Roman-Ivanitch/Project.9.class/dimensional_drawing/gusset/плохой.jpg

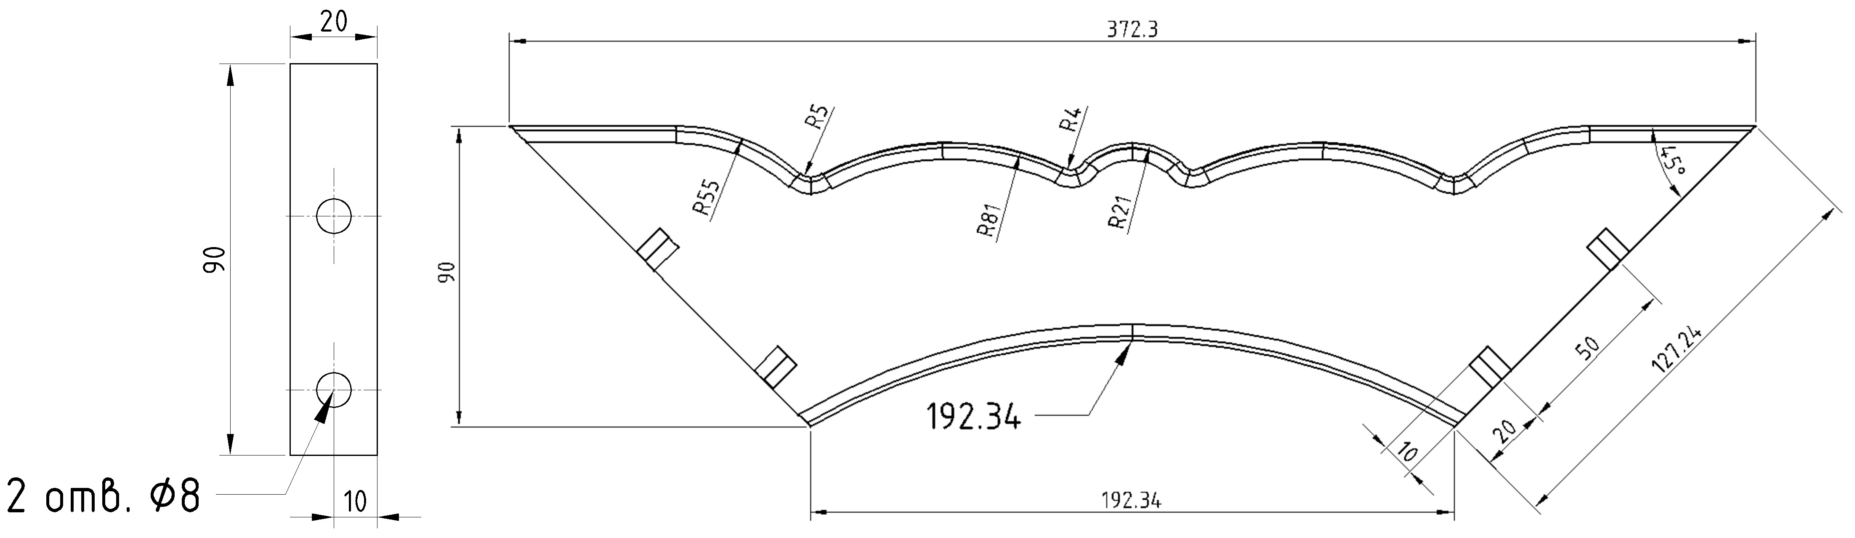
dimensional_drawing/gusset/плохой.jpg
