Roman-Ivanitch/Project.9.class/dimensional_drawing/gusset/плохой_чертёж.png

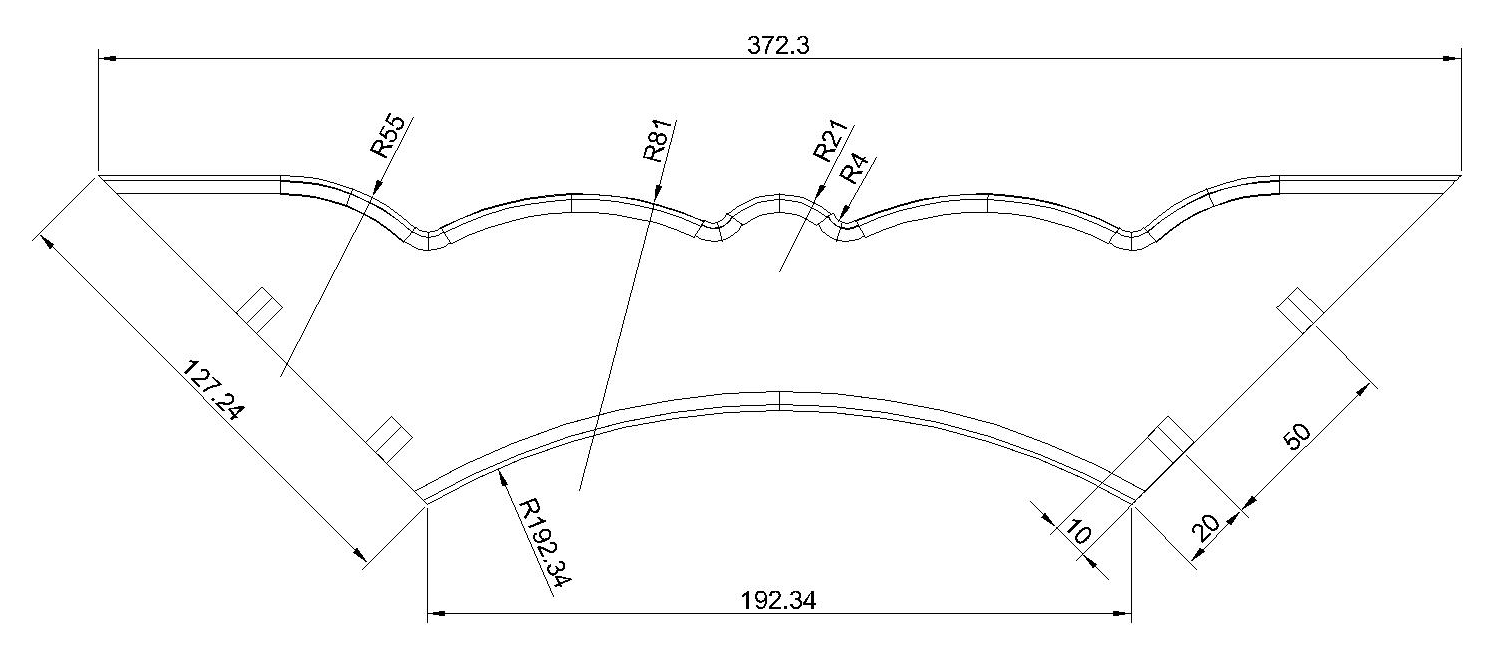
dimensional_drawing/gusset/плохой_чертёж.png
