Roman-Ivanitch/Project.9.class/dimensional_drawing/gusset/чертёж_косынки1.png

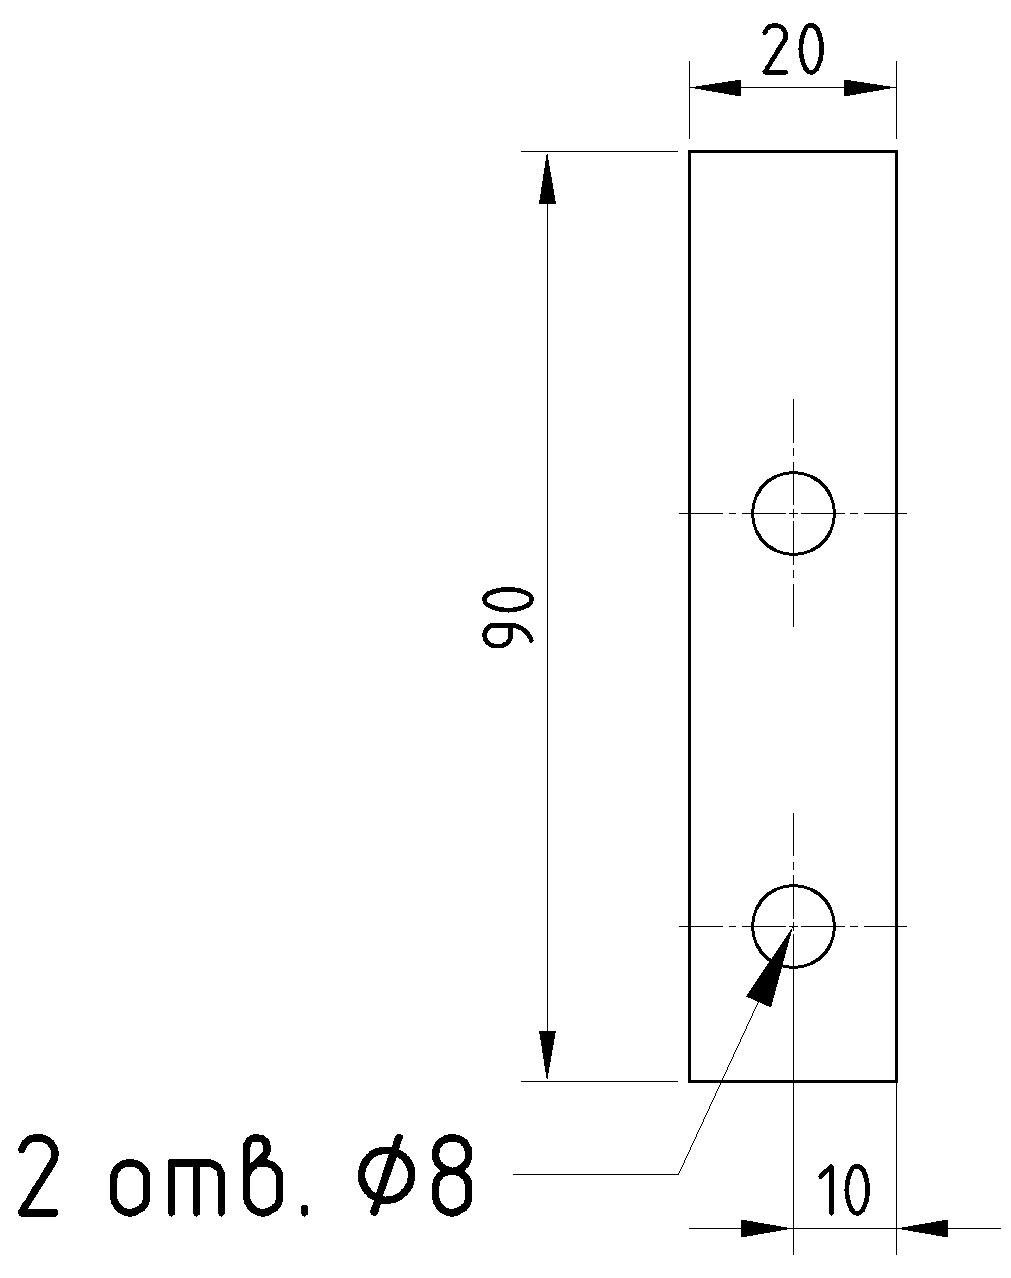
dimensional_drawing/gusset/чертёж_косынки1.png
