Roman-Ivanitch/Project.9.class/dimensional_drawing/lamp/вид_сверху.png

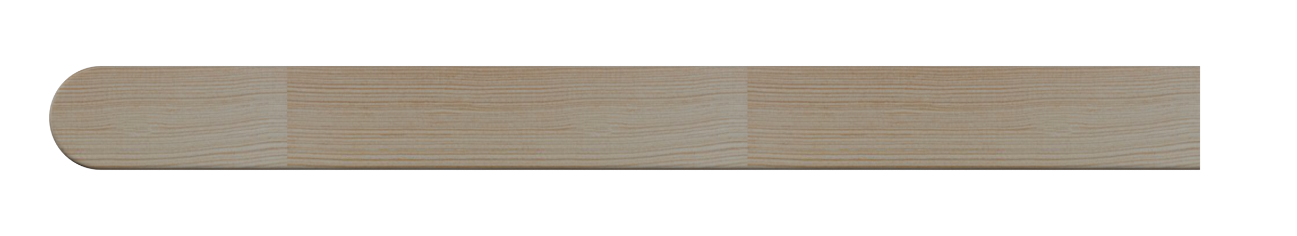
dimensional_drawing/lamp/вид_сверху.png
