Roman-Ivanitch/Project.9.class/dimensional_drawing/lamp/вид_слева.png

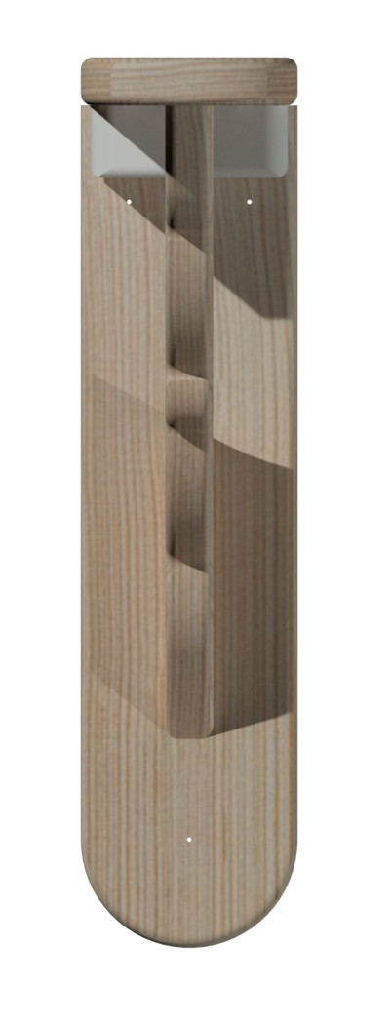
dimensional_drawing/lamp/вид_слева.png
