Roman-Ivanitch/Project.9.class/dimensional_drawing/lamp/вид_снизу.png

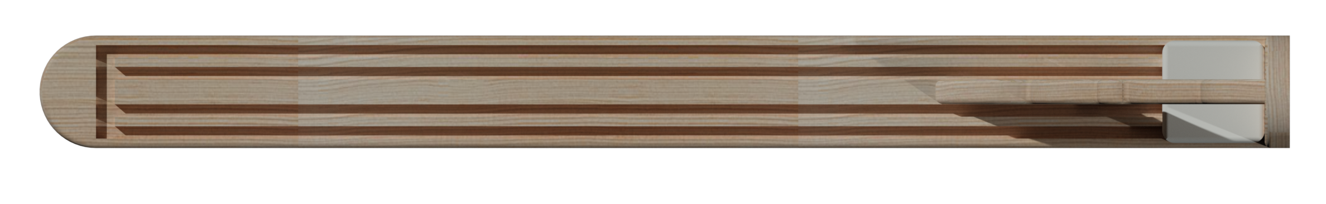
dimensional_drawing/lamp/вид_снизу.png
