Roman-Ivanitch/Project.9.class/elecktronika/Schematic_10 class_2021-09-17.png

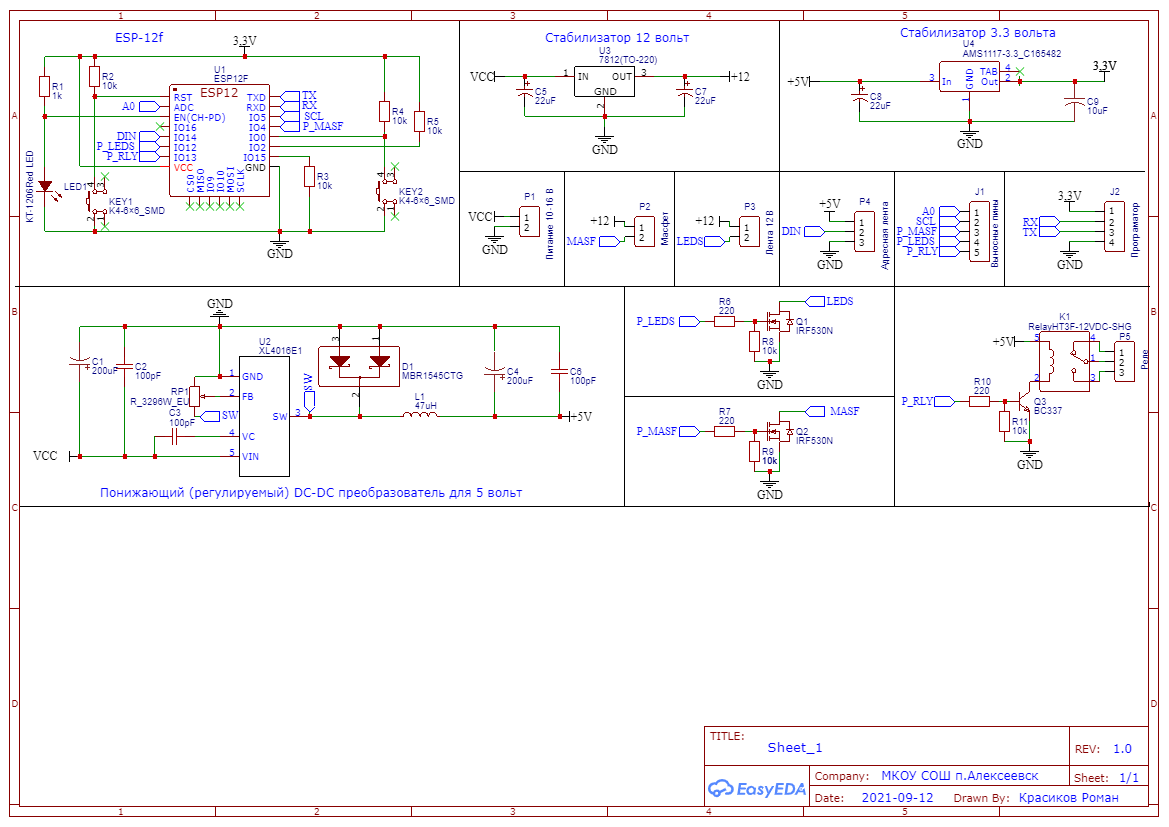
elecktronika/Schematic_10 class_2021-09-17.png
