Roman-Ivanitch/Project.9.class/images/colors/blue.jpg

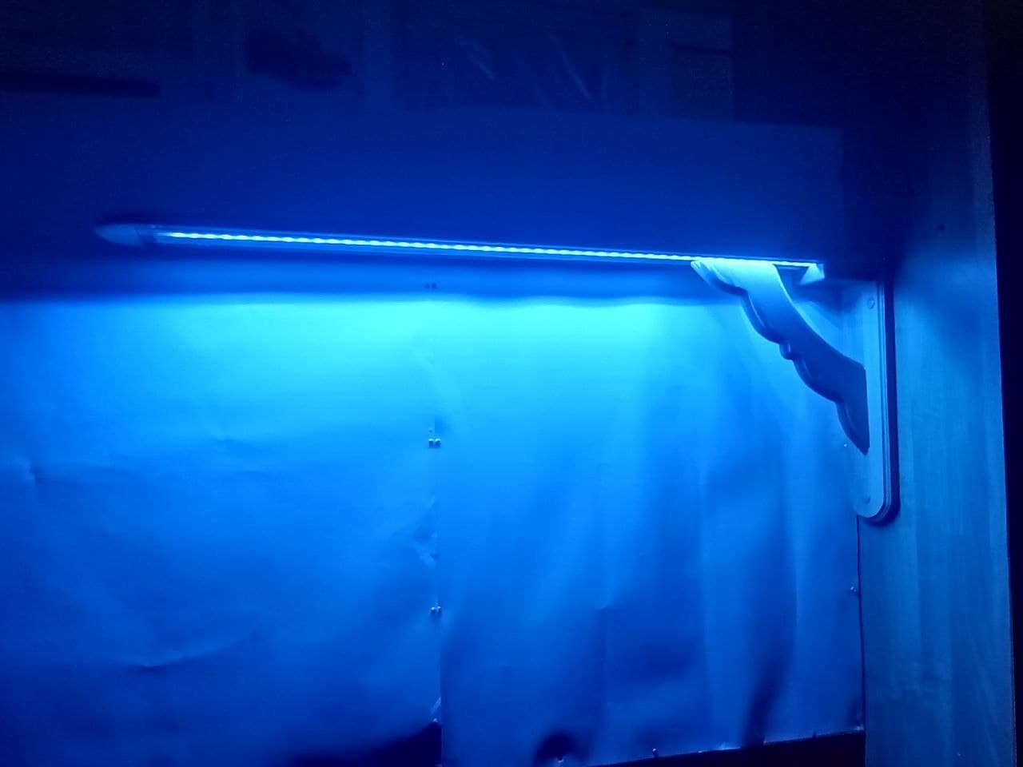
images/colors/blue.jpg
