Roman-Ivanitch/Project.9.class/images/colors/green.jpg

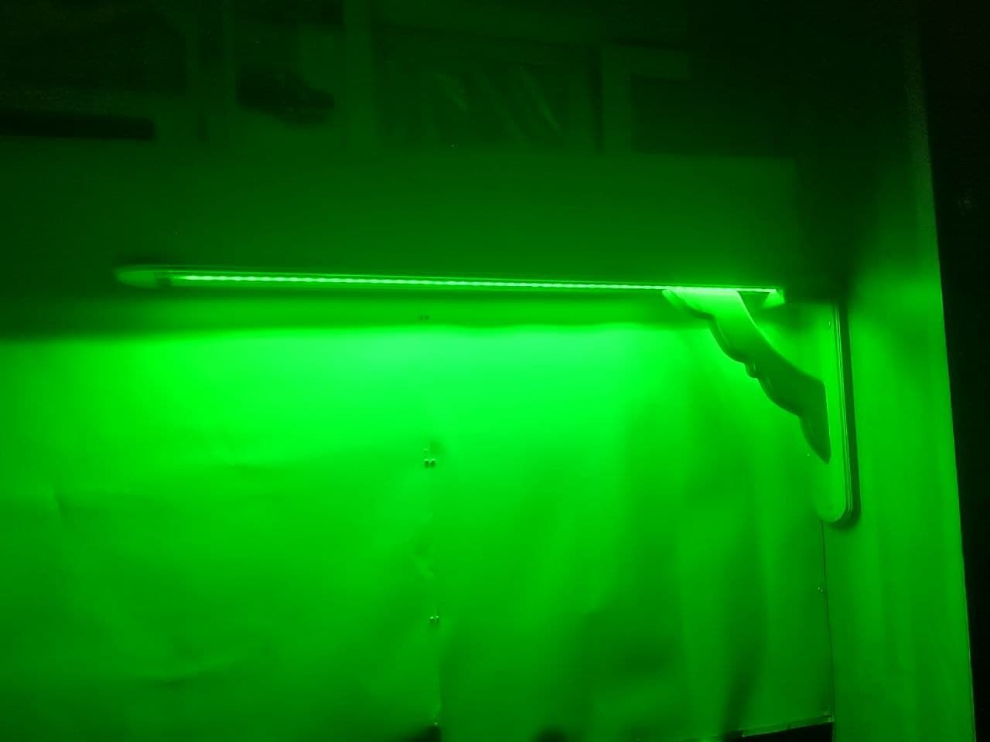
images/colors/green.jpg
