Roman-Ivanitch/Project.9.class/images/colors/orange.jpg

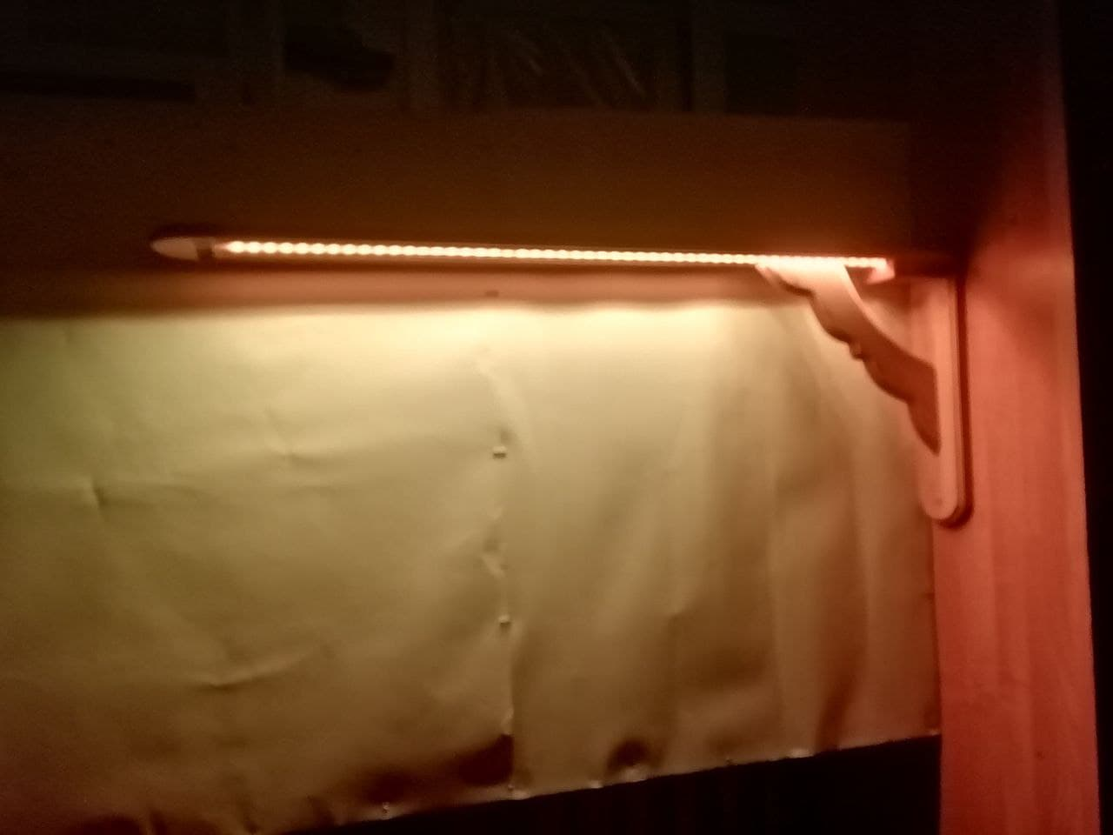
images/colors/orange.jpg
