Roman-Ivanitch/Project.9.class/images/colors/purple.jpg

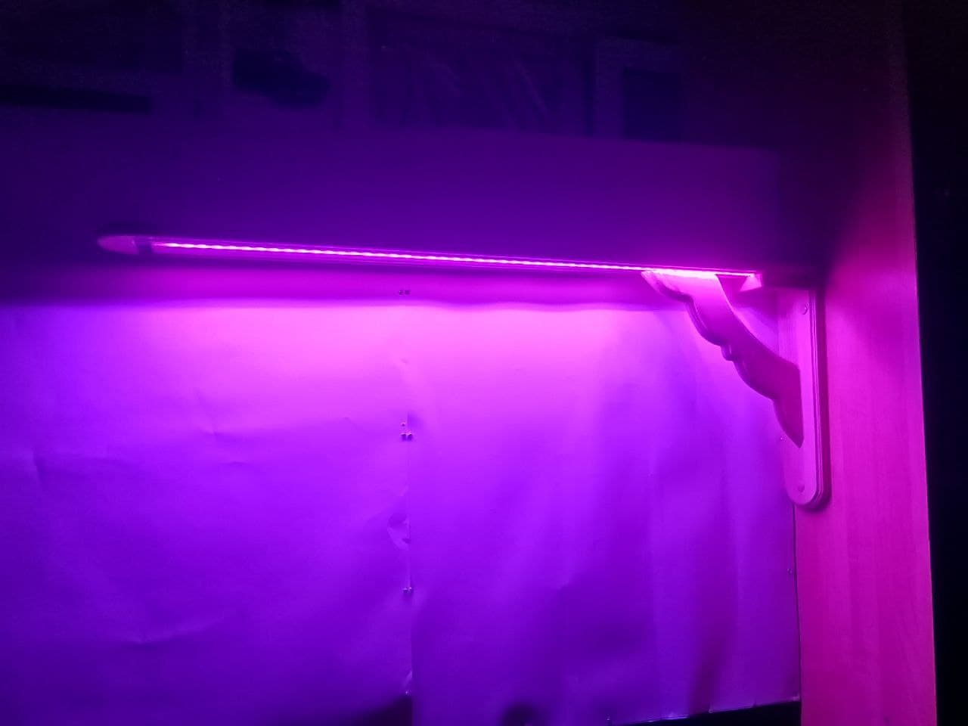
images/colors/purple.jpg
