Roman-Ivanitch/Project.9.class/images/colors/red..jpg

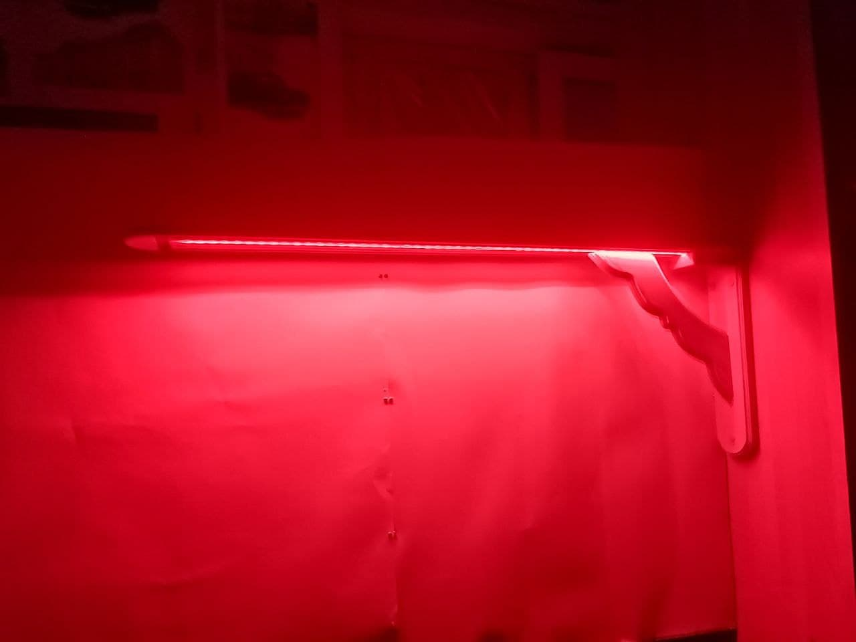
images/colors/red..jpg
