Roman-Ivanitch/Project.9.class/images/colors/turquoise.jpg

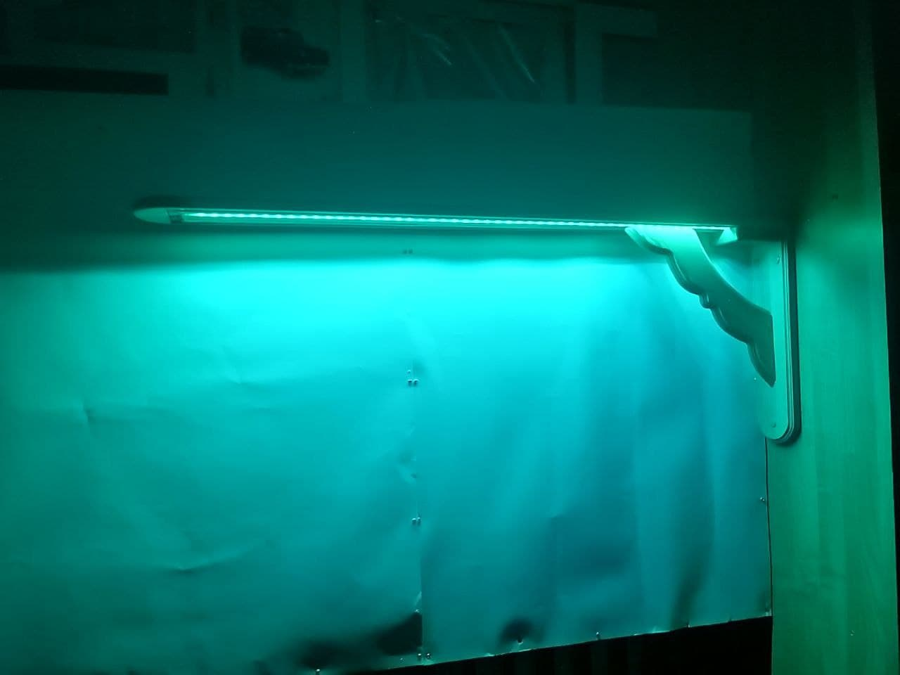
images/colors/turquoise.jpg
