Roman-Ivanitch/Project.9.class/images/colors/white.jpg

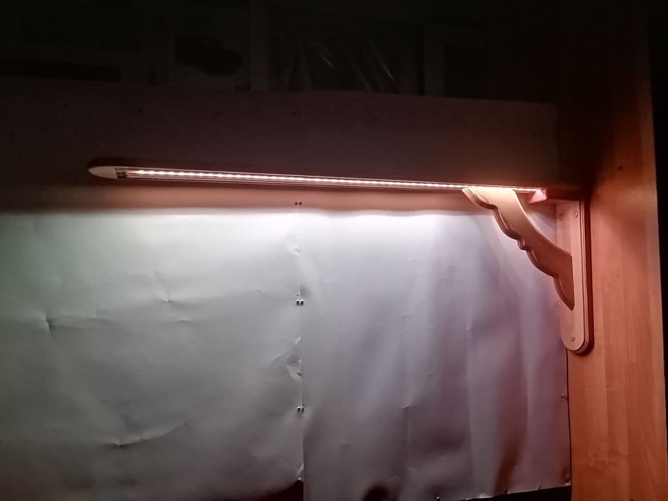
images/colors/white.jpg
