Roman-Ivanitch/Project.9.class/images/colors/yellow.jpg

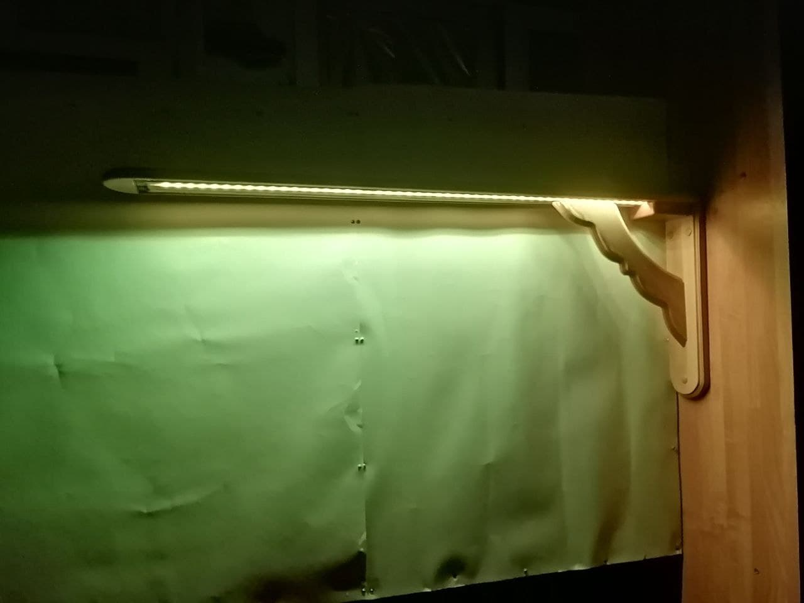
images/colors/yellow.jpg
