Roman-Ivanitch/Project.9.class/images/effects/log_up.png

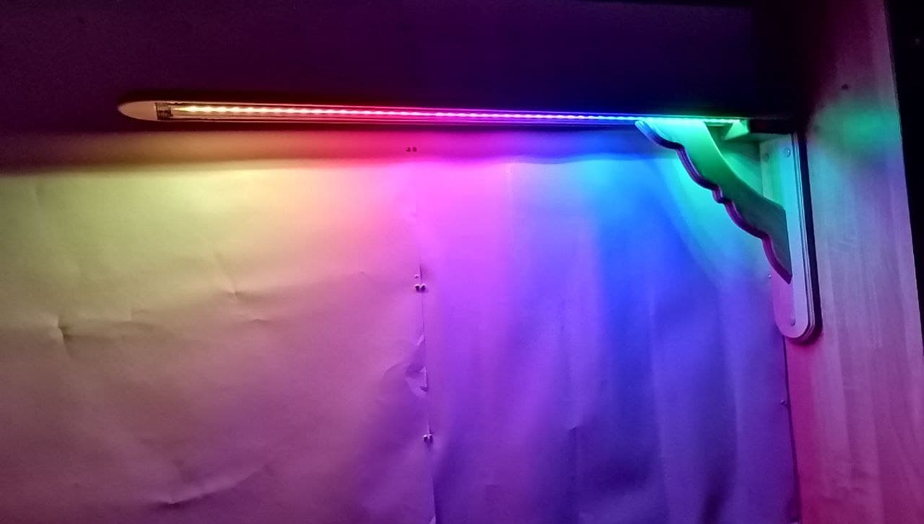
images/effects/log_up.png
