Roman-Ivanitch/Project.9.class/images/effects/red-blue.jpg

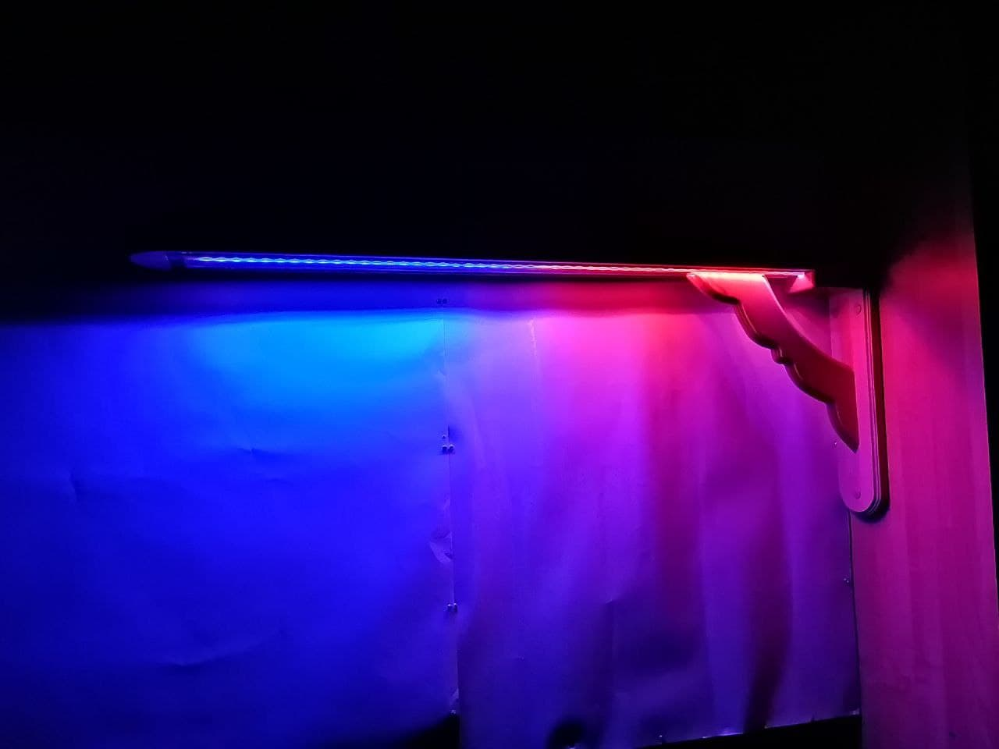
images/effects/red-blue.jpg
