Roman-Ivanitch/Project.9.class/images/effects/RGBpropeller.jpg

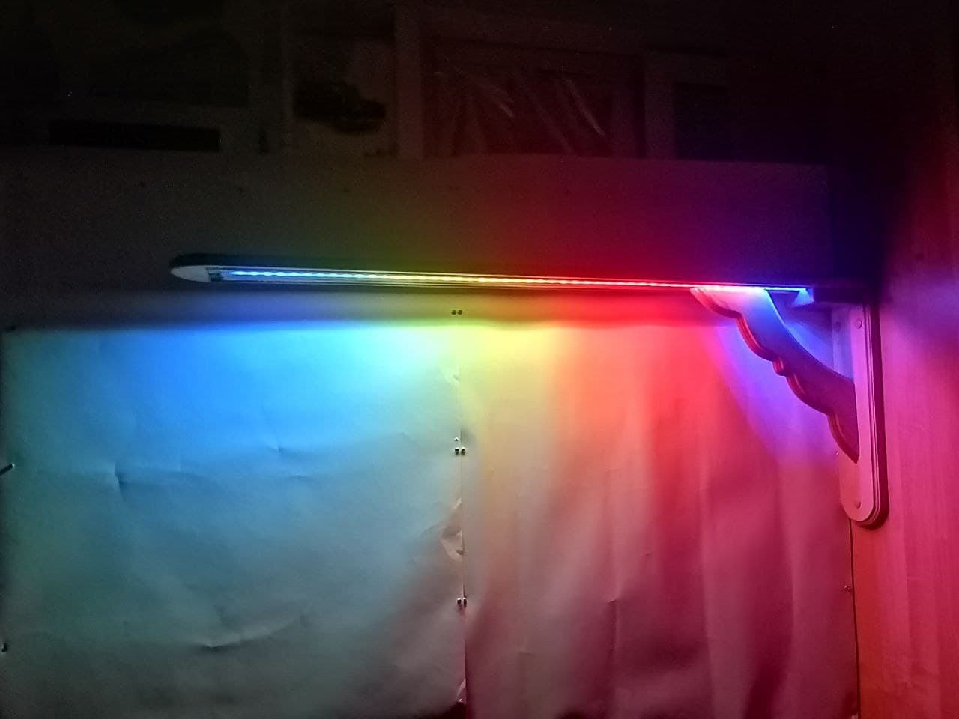
images/effects/RGBpropeller.jpg
