Roman-Ivanitch/Project.9.class/images/electronic/4.Замер напряжения.jpg

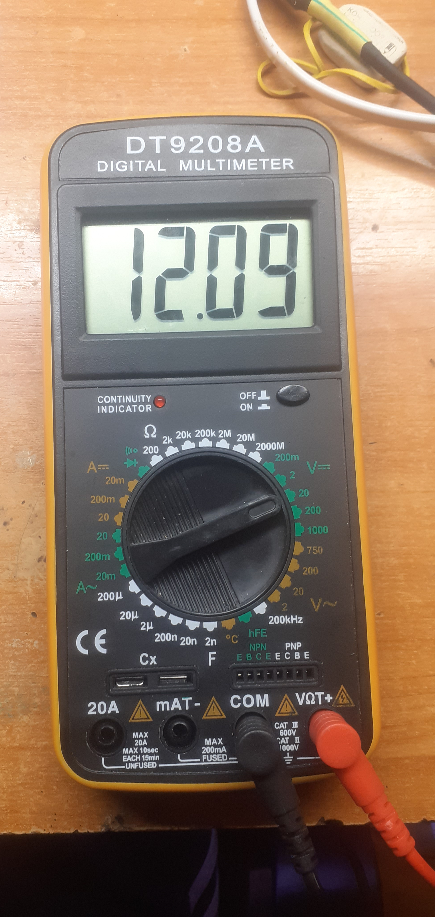
images/electronic/4.Замер напряжения.jpg
