Roman-Ivanitch/Project.9.class/images/electronic/5.Замер силы тока.jpg

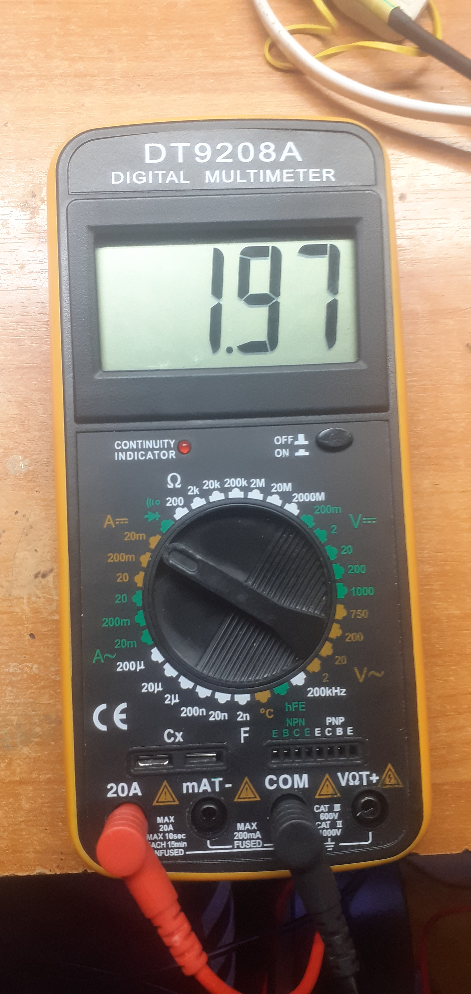
images/electronic/5.Замер силы тока.jpg
