Roman-Ivanitch/Project.9.class/images/electronic/led.jpg

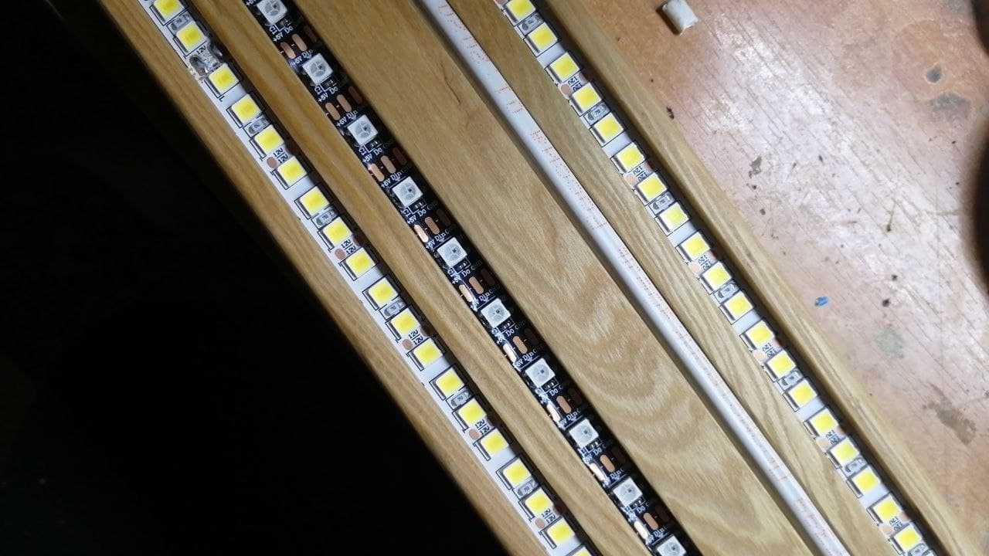
images/electronic/led.jpg
