Roman-Ivanitch/Project.9.class/images/electronic/лицевая.png

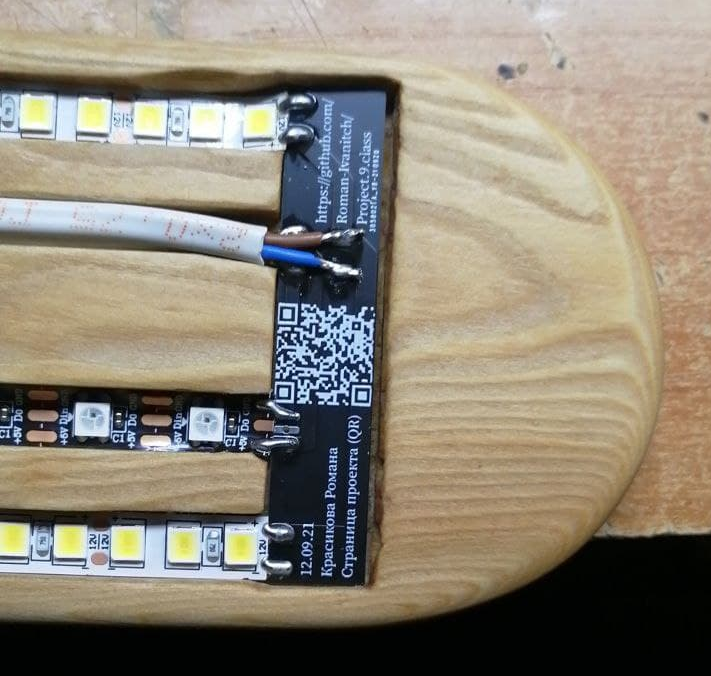
images/electronic/лицевая.png
