Roman-Ivanitch/Project.9.class/images/electronic/подраспредкоробкой.jpg

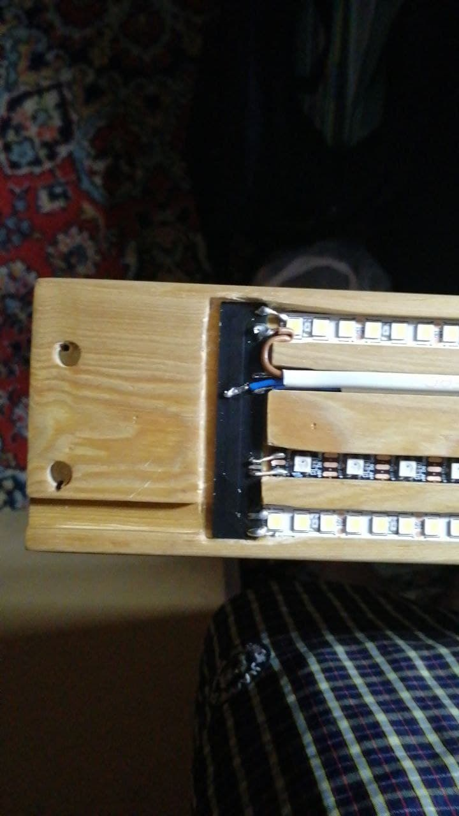
images/electronic/подраспредкоробкой.jpg
