Roman-Ivanitch/Project.9.class/images/electronic/разметка.jpg

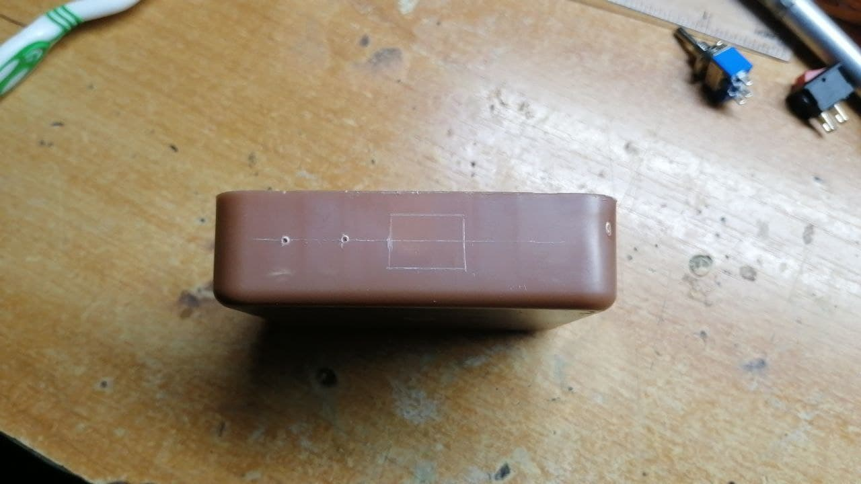
images/electronic/разметка.jpg
