Roman-Ivanitch/Project.9.class/images/lamp/1.Вид на рабочем месте.jpg

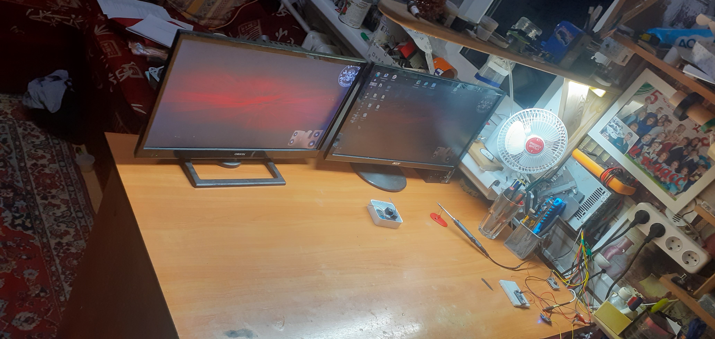
images/lamp/1.Вид на рабочем месте.jpg
