Roman-Ivanitch/Project.9.class/images/lamp/2.Общий вид лампы.jpg

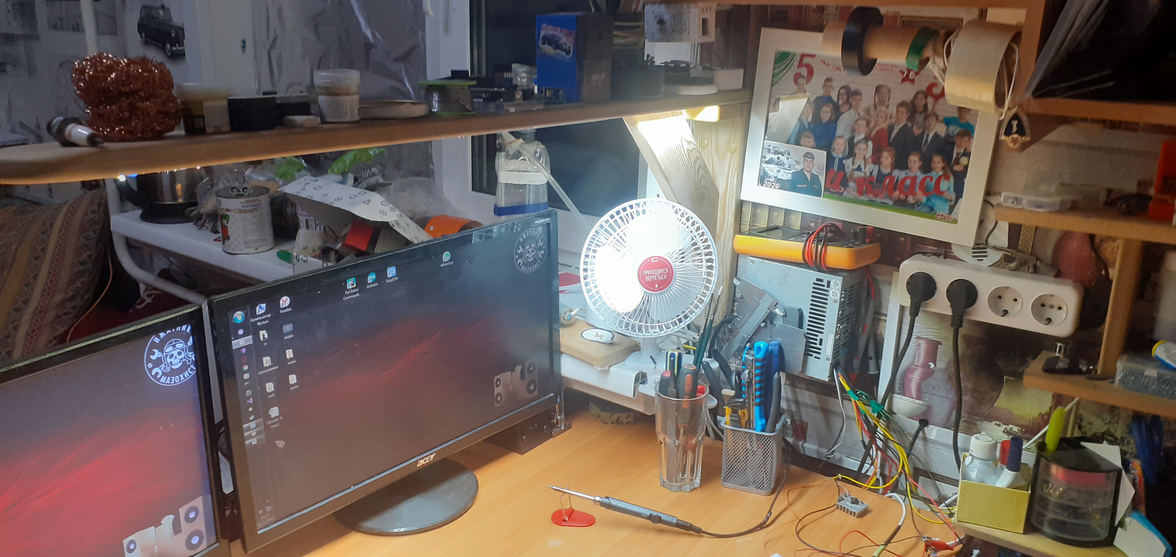
images/lamp/2.Общий вид лампы.jpg
