Roman-Ivanitch/Project.9.class/images/lamp/3.Общий вид лампы 2.jpg

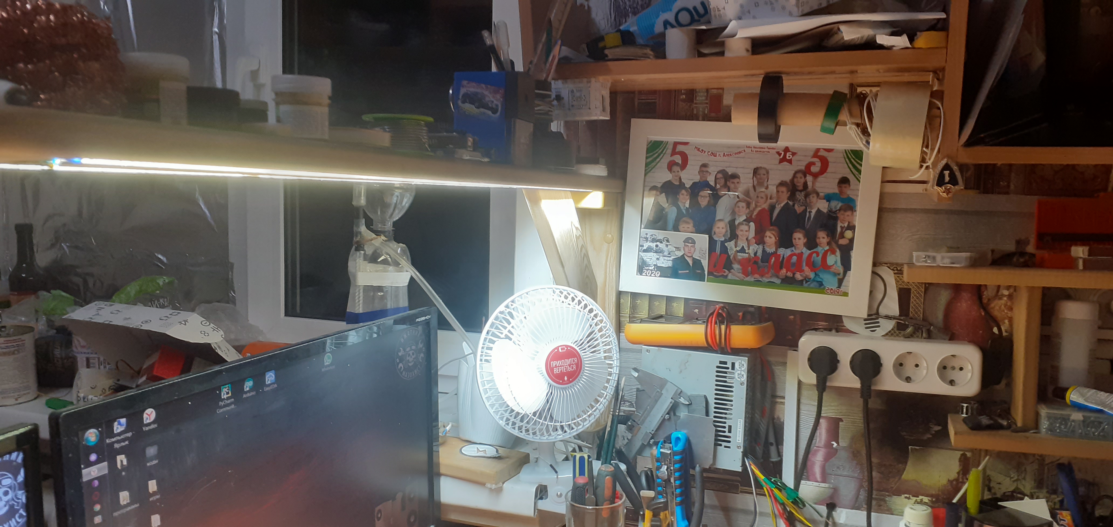
images/lamp/3.Общий вид лампы 2.jpg
