Roman-Ivanitch/Project.9.class/images/lamp/9.Все детали в сборе.jpg

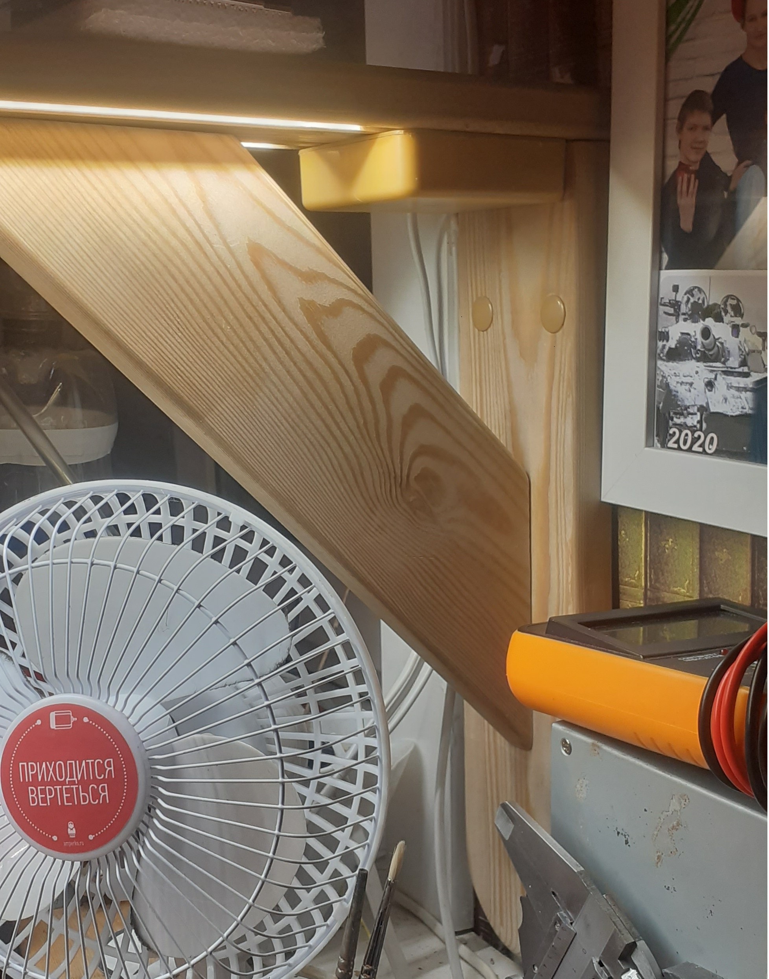
images/lamp/9.Все детали в сборе.jpg
