Roman-Ivanitch/Project.9.class/images/lamp/10.Все детали в сборе 2.jpg

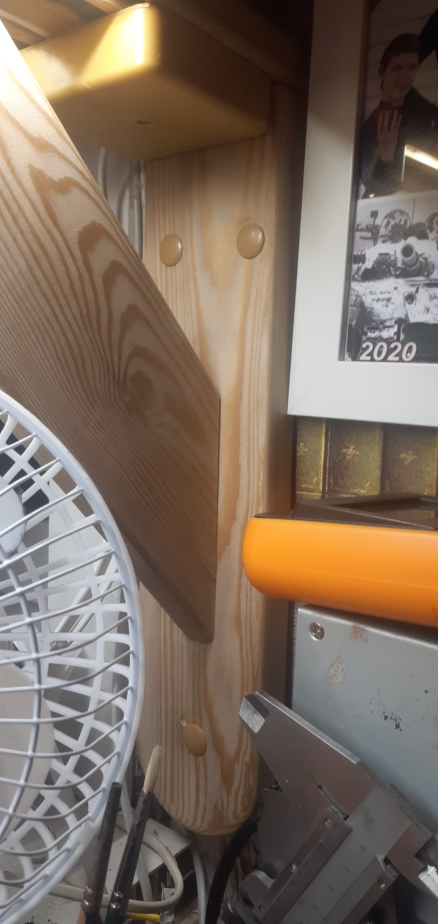
images/lamp/10.Все детали в сборе 2.jpg
