Roman-Ivanitch/Project.9.class/images/lamp/below.jpg

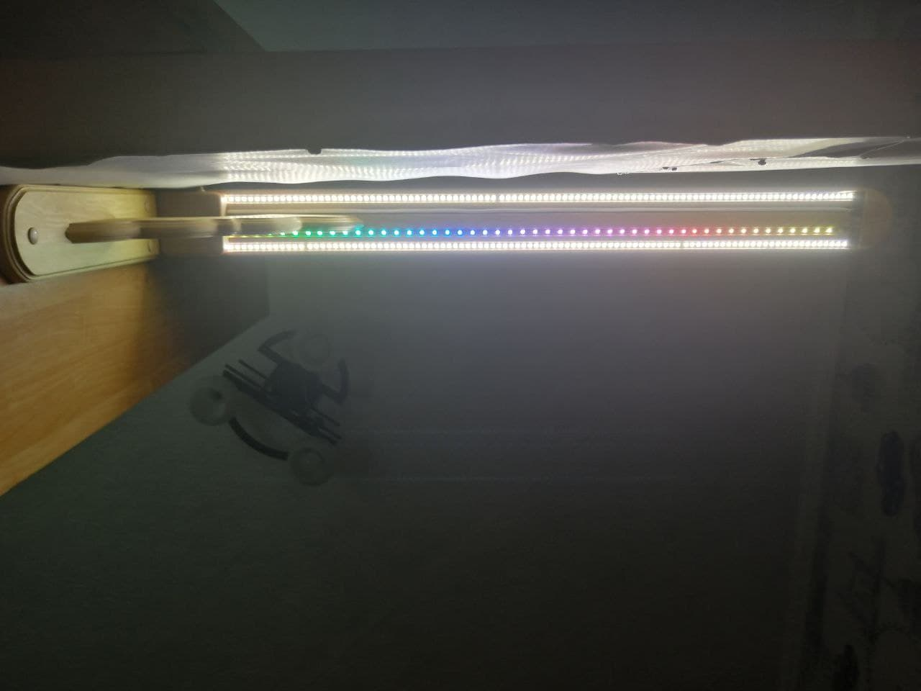
images/lamp/below.jpg
