Roman-Ivanitch/Project.9.class/images/lamp/front view.jpg

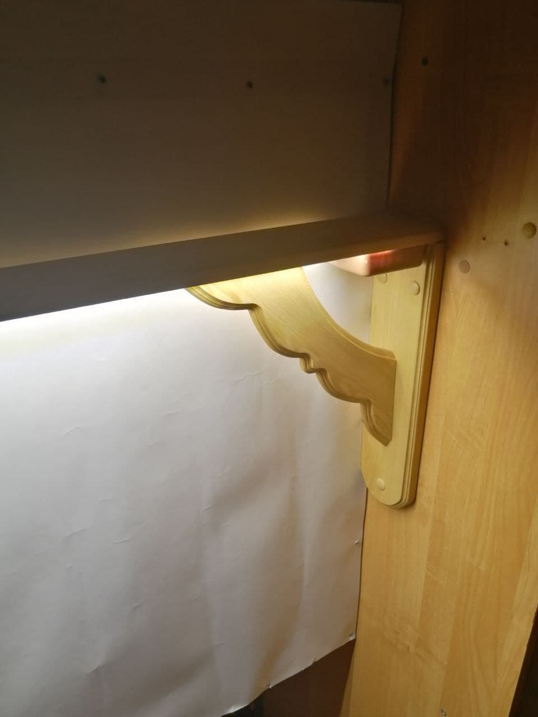
images/lamp/front view.jpg
