Roman-Ivanitch/Project.9.class/images/lamp/front_view.jpg

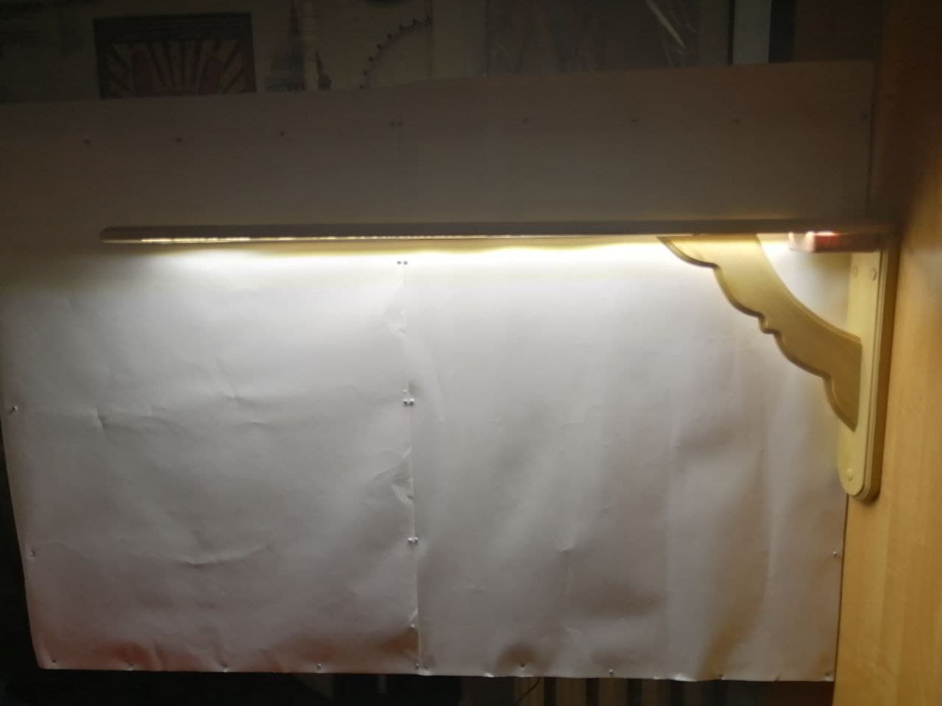
images/lamp/front_view.jpg
