Roman-Ivanitch/Project.9.class/images/lamp/lamp_.jpg

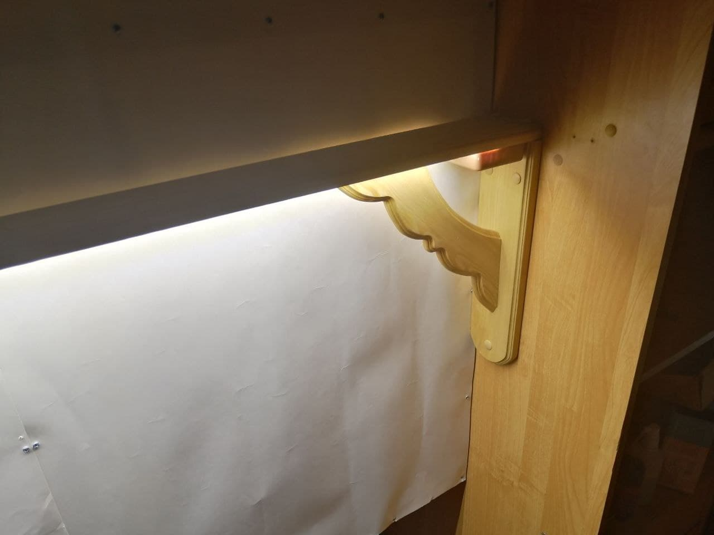
images/lamp/lamp_.jpg
