Roman-Ivanitch/Project.9.class/images/lamp/light_up.png

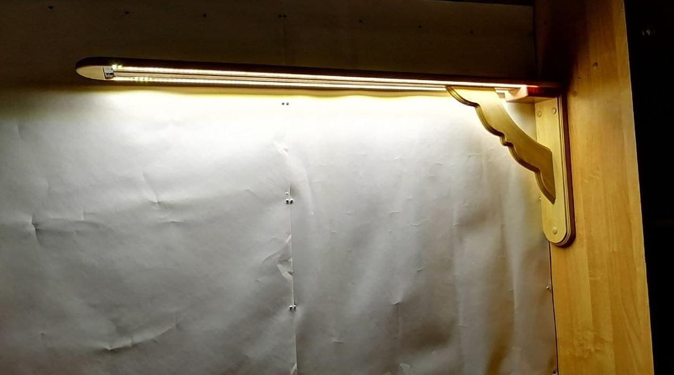
images/lamp/light_up.png
