Roman-Ivanitch/Project.9.class/images/lamp/mistake.jpg

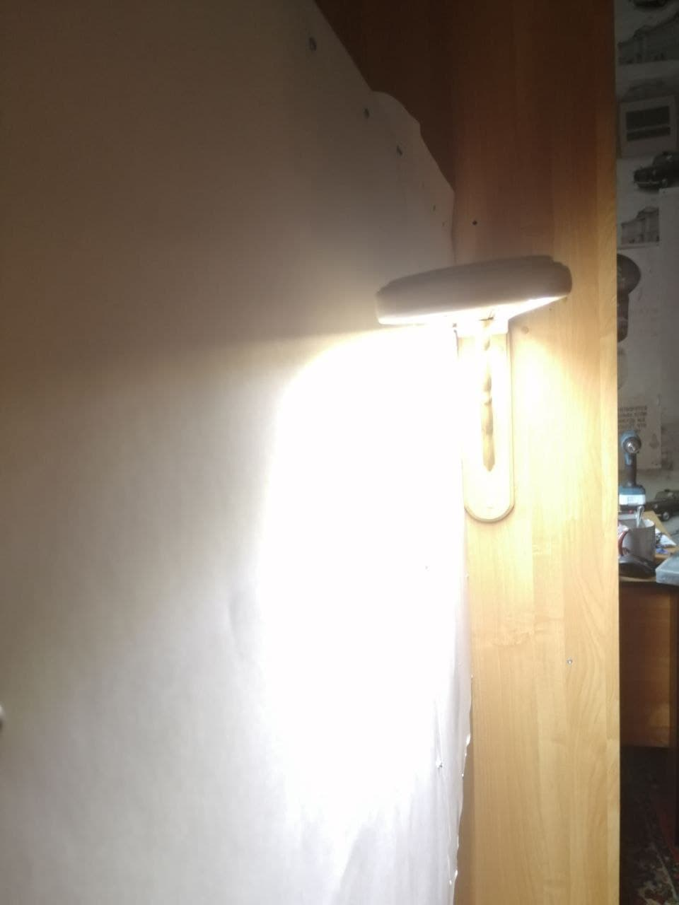
images/lamp/mistake.jpg
