Roman-Ivanitch/Project.9.class/images/light.png

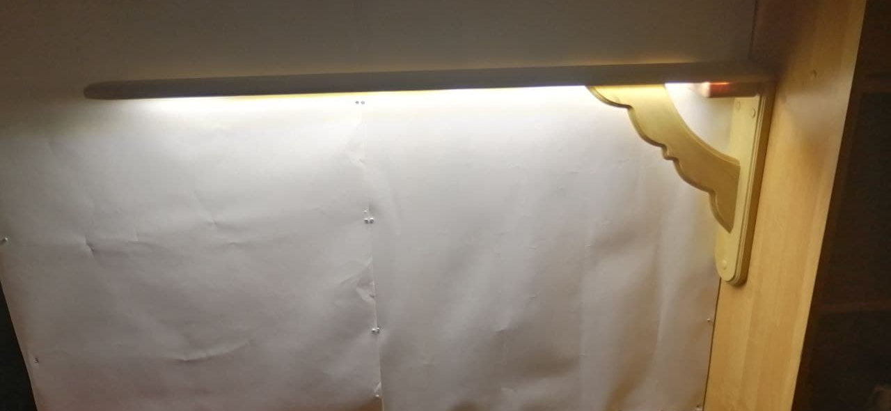
images/light.png
