Roman-Ivanitch/Project.9.class/images/log.png

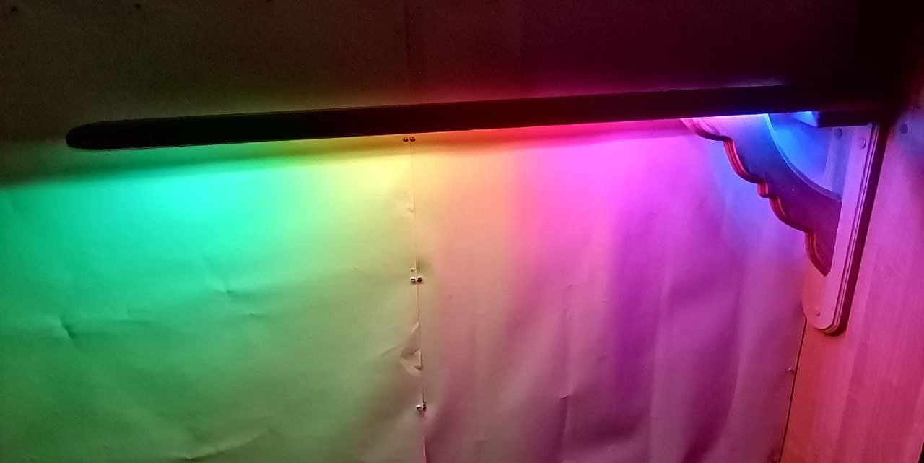
images/log.png
