Roman-Ivanitch/Project.9.class/images/диаграмма.png

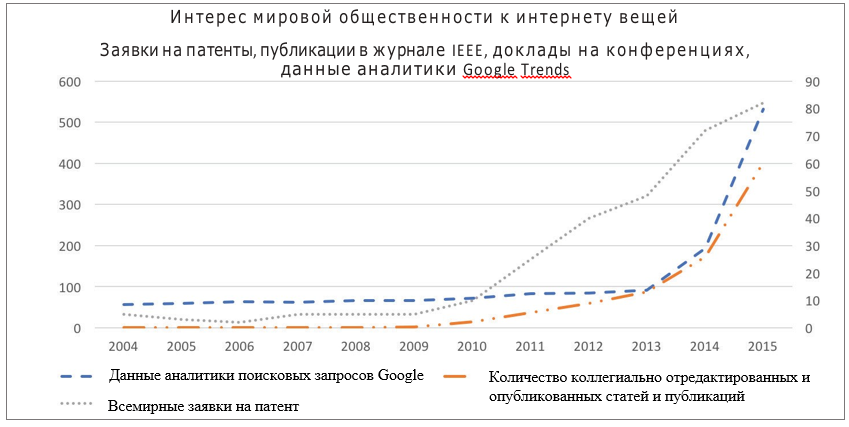
images/диаграмма.png
